ajn96/iSensor-SPI-Buffer/img/iSensor_spi_buffer_revb_bot.png

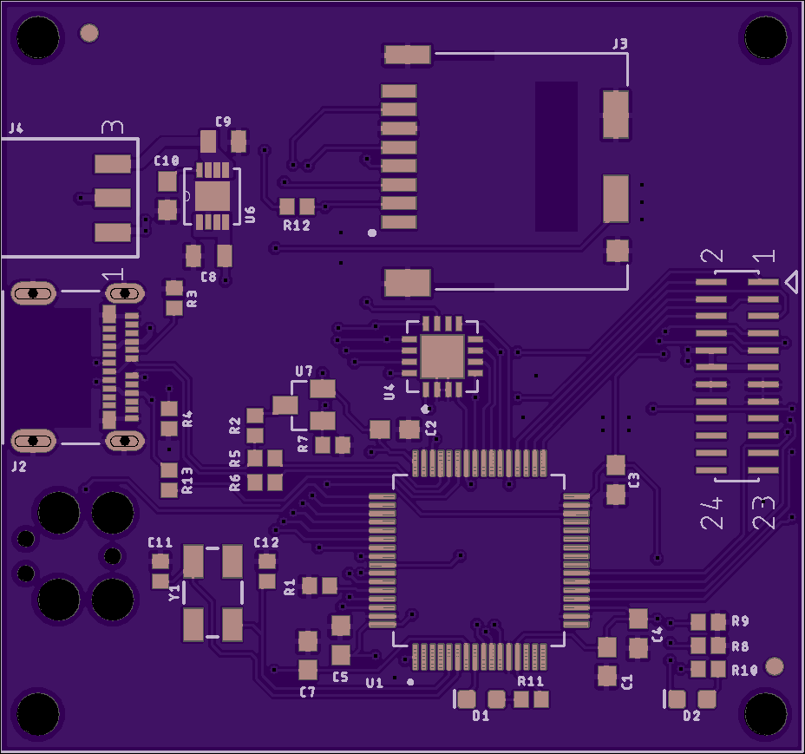
img/iSensor_spi_buffer_revb_bot.png
