ajn96/iSensor-SPI-Buffer/img/iso_image.jpg

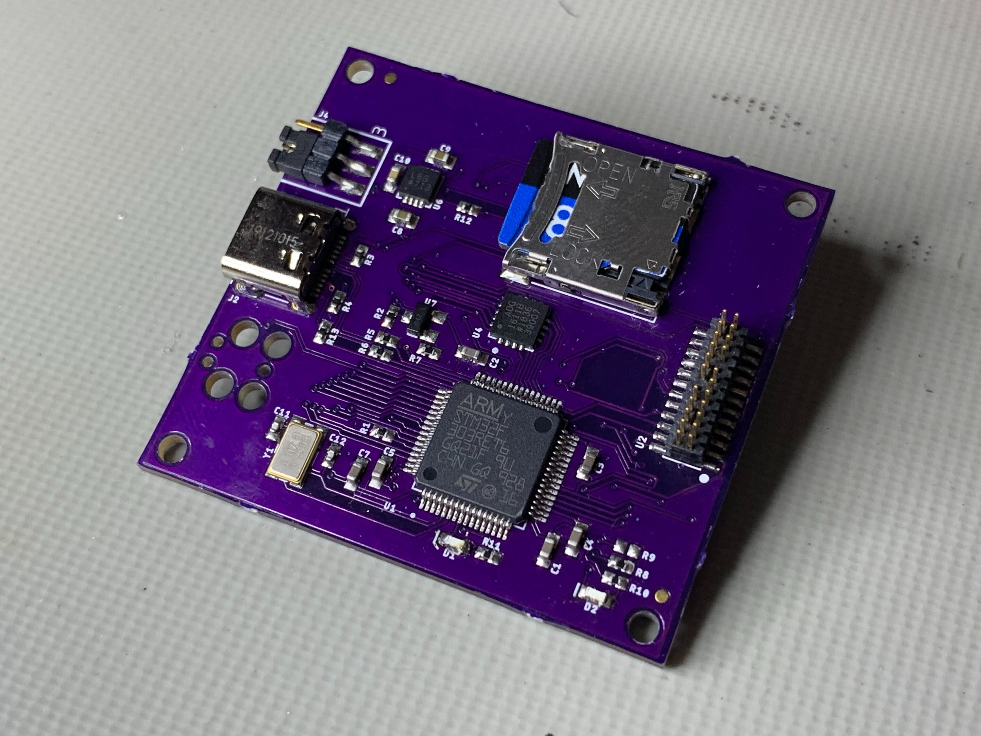
img/iso_image.jpg
