ajn96/iSensor-SPI-Buffer/img/rev_c_image.jpg

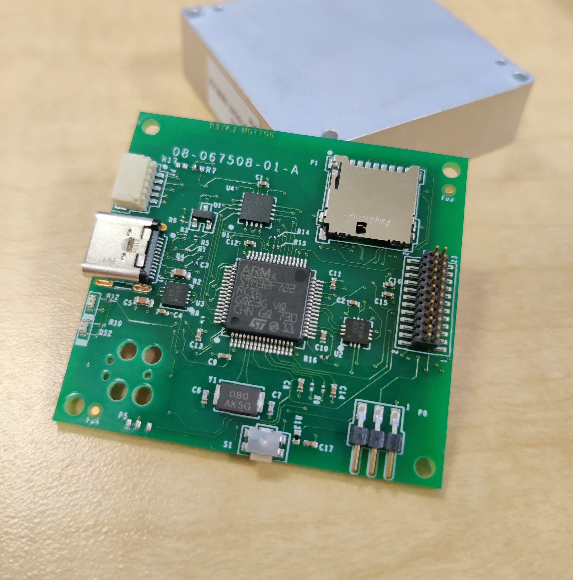
img/rev_c_image.jpg
