ajn96/iSensor-SPI-Buffer/img/usb_view.jpg

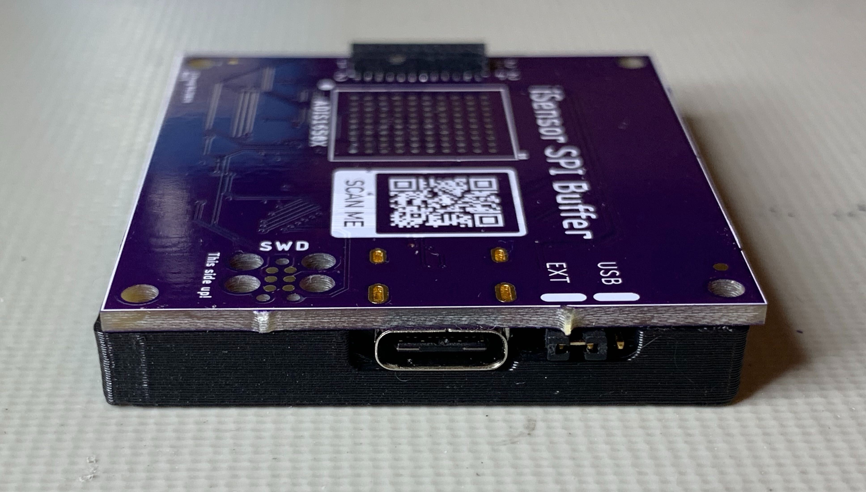
img/usb_view.jpg
