ajn96/iSensor-SPI-Buffer/firmware/Core/Src/isr.c

/**
  * Copyright (c) Analog Devices Inc, 2020
  * All Rights Reserved.
  *
  * @file		isr.c
  * @date		4/27/2020
  * @author		A. Nolan (alex.nolan@analog.com)
  * @brief		iSensor-SPI-Buffer interrupt service routines
 **/

#include "reg.h"
#include "imu.h"
#include "isr.h"
#include "buffer.h"
#include "user_spi.h"
#include "dio.h"
#include "flash.h"
#include "main.h"
#include "data_capture.h"
#include "timer.h"

/* Private function prototypes */
static void FinishImuBurst();
static void ProcessSPITransaction(uint32_t rx);

/** Current capture size (in 16 bit words). Global scope */
volatile uint32_t g_wordsPerCapture;

/** Track if there is currently a capture in progress */
volatile uint32_t g_captureInProgress = 0u;

/** Pointer to buffer element which is being populated */
static uint8_t* BufferElementHandle;

/** Pointer to buffer data signature within buffer element which is being populated */
static uint16_t* BufferSigHandle;

/** Track number of words captured within current buffer entry */
static volatile uint32_t WordsCaptured;

/** Buffer signature */
static uint32_t BufferSignature;

/** Flag to track if IMU burst DMA is done */
static volatile uint32_t ImuDMADone = 0;

/**
  * @brief IMU data ready ISR. Kicks off data capture process.
  *
  * @return void
  *
  * All four DIOx_Master pins map to this interrupt handler. Only one
  * should be enabled as an interrupt source at a time. This interrupt
  * also handles PPS input signals for DIO2-4. The EXTI pending interrupt
  * register (PR) can be used to identify if the interrupt is coming from
  * a PPS strobe or an IMU data ready signal.
  */
void EXTI9_5_IRQHandler()
{
	/* EXTI pending request register */
	static uint32_t EXTI_PR;

	/* Microsecond sample time stamp */
	static uint32_t SampleTimestampUs;

	/* Second sample time stamp */
	static uint32_t SampleTimestampS;

	/* Clear exti PR register (lines 5-9) */
	EXTI_PR = EXTI->PR;
	EXTI->PR = (0x1F << 5);

	/* Check if is PPS interrupt */
	if(EXTI_PR & (PPS_INT_MASK))
	{
		/* Increment PPS counter and clear microsecond timestamp */
		Timer_Increment_PPS_Time();
	}

	/* Exit if no data ready interrupt */
	if(!(EXTI_PR & (DATA_READY_INT_MASK)))
	{
		return;
	}

	/* If capture in progress then set error flag and exit */
	if(g_captureInProgress)
	{
		/* If SPI DMA and timer 4 are not running then capture is not actually in progress */
		if((g_dma_spi1_tx.Instance->CNDTR > 0)||(g_dma_spi1_rx.Instance->CNDTR > 0)||(TIM4->CR1 & 0x1))
		{
			g_captureInProgress = 1;
		}
		else
		{
			g_captureInProgress = 0;
		}
		g_regs[STATUS_0_REG] |= STATUS_OVERRUN;
		g_regs[STATUS_1_REG] = g_regs[STATUS_0_REG];
		return;
	}

	/* If buffer element cannot be added then exit */
	if(!Buffer_Can_Add_Element())
		return;

	/* Get the sample timestamp */
	SampleTimestampUs = Timer_Get_Microsecond_Timestamp();
	SampleTimestampS = Timer_Get_PPS_Timestamp();

	/* Get element handle */
	BufferElementHandle = Buffer_Add_Element();

	/* Add timestamp to buffer */
	*(uint32_t *) BufferElementHandle = SampleTimestampS;
	*(uint32_t *) (BufferElementHandle + 4) = SampleTimestampUs;

	/* Set signature to timestamp value initially */
	BufferSignature = SampleTimestampS & 0xFFFF;
	BufferSignature += (SampleTimestampS >> 16);
	BufferSignature += SampleTimestampUs & 0xFFFF;
	BufferSignature += (SampleTimestampUs >> 16);

	/* Set buffer signature handle */
	BufferSigHandle = (uint16_t *) (BufferElementHandle + 8);

	/* Offset buffer element handle by 10 bytes (timestamp + sig) */
	BufferElementHandle += 10;

	/* Set flag indicating capture is running */
	g_captureInProgress = 1;

	if(g_regs[BUF_CONFIG_REG] & BUF_CFG_IMU_BURST)
	{
		ImuDMADone = 0;
		IMU_Start_Burst(BufferElementHandle);
	}
	else
	{
		/* Register SPI data capture */

		/* Set words captured to 0 */
		WordsCaptured = 0;

		/*Set timer value to 0 */
		TIM4->CNT = 0;
		/* Enable timer */
		TIM4->CR1 |= 0x1;
		/* Clear timer interrupt flag */
		TIM4->SR &= ~TIM_SR_UIF;

		/* Send first 16 bit word */
		TIM3->CR1 &= ~0x1;
		TIM3->CNT = 0;
		TIM3->CR1 |= 0x1;
		SPI1->DR = g_regs[BUF_WRITE_0_REG];
	}
}

/**
  * @brief EXTI 4 interrupt handler.
  *
  * @return void
  *
  * This interrupt is generated by a PPS signal applied to
  * DIO1 only. All other PPS inputs generate an EXTI9_5 interrupt
  */
void EXTI4_IRQHandler()
{
	/* Clear pending interrupts */
	EXTI->PR = (1 << 4);

	/* Increment PPS timestamp */
	Timer_Increment_PPS_Time();
}

/**
  * @brief IMU SPI timer ISR.
  *
  * @return void
  *
  * This interrupt retrieves the SPI data read on the previous SPI transaction. It
  * then starts the next SPI transaction (if needed) and returns.
  */
void TIM4_IRQHandler()
{
	/** SPI MISO data */
	static uint32_t SpiMiso;

	/* Clear timer interrupt flag */
	TIM4->SR &= ~TIM_SR_UIF;

	/* Reset timer count. Want to reset it to give a ~0.7us offset */
	TIM4->CNT = 50;

	/* Disable CS timer */
	TIM3->CR1 = 0;
	TIM3->CNT = 0xFFFF;

	if(!g_captureInProgress)
	{
		/* Disable timers */
		TIM4->CR1 &= ~0x1;
		return;
	}

	/* Wait for SPI rx done (running in master mode, shouldn't be an issue) */
	while(!(SPI1->SR & SPI_SR_RXNE));

	/* Grab SPI data from last transaction */
	SpiMiso = SPI1->DR;

	/* Add to signature */
	BufferSignature += SpiMiso;

	BufferElementHandle[0] = (SpiMiso & 0xFF);
	BufferElementHandle[1] = (SpiMiso >> 8);
	BufferElementHandle += 2;

	/* Increment words captured count */
	WordsCaptured++;

	if(WordsCaptured < g_wordsPerCapture)
	{
		/* Restart PWM timer for CS */
		TIM3->CR1 |= 0x1;
		/* Load SPI transmit reg */
		SPI1->DR = g_regs[BUF_WRITE_0_REG + WordsCaptured];
	}
	else
	{
		/* Disable timers and ensure CS is high */
		TIM4->CR1 &= ~0x1;
		TIM3->CR1 &= ~0x1;
		TIM3->CNT = 0xFFFF;

		/* Save final signature */
		BufferSigHandle[0] = BufferSignature;

		/* Update buffer count regs with new count */
		g_regs[BUF_CNT_0_REG] = g_bufCount;
		g_regs[BUF_CNT_1_REG] = g_regs[BUF_CNT_0_REG];

		/* Mark capture as done */
		g_captureInProgress = 0;
	}
}

/**
  * @brief This function handles DMA1 channel2 global interrupt (spi1 (IMU) Rx).
  *
  * @return void
  *
  * This DMA is used to receive data from an IMU during a burst data capture.
  * In order for an IMU data capture to be complete, this DMA channel and the
  * transmit DMA channel have to both finish their work. In general, this channel
  * will finish last.
  **/
void DMA1_Channel2_IRQHandler(void)
{
	uint32_t flags = g_dma_spi1_rx.DmaBaseAddress->ISR;

	/* Clear interrupt enable */
	g_dma_spi1_rx.Instance->CCR &= ~(DMA_IT_TC | DMA_IT_TE);

	/* Clear interrupt flags */
	g_dma_spi1_rx.DmaBaseAddress->IFCR = (DMA_FLAG_TC1|DMA_FLAG_TE1) << g_dma_spi1_rx.ChannelIndex;

	/* Check for error interrupt */
	if(flags & (DMA_FLAG_TE1 << g_dma_spi1_rx.ChannelIndex))
	{
		g_regs[STATUS_0_REG] |= STATUS_DMA_ERROR;
		g_regs[STATUS_1_REG] = g_regs[STATUS_0_REG];
		FinishImuBurst();
	}

	/* Check if both interrupts complete */
	if(ImuDMADone == 0)
	{
	  ImuDMADone = 1;
	}
	else
	{
	  /* Both are done */
	  FinishImuBurst();
	}
}

/**
  * @brief This function handles DMA1 channel3 global interrupt (spi1 (IMU) Tx).
  *
  * @return void
  *
  * This DMA is used to transmit the write data array to the IMU during a burst
  * data capture. It runs in parallel with DMA channel 2 to achieve full duplex burst.
  */
void DMA1_Channel3_IRQHandler(void)
{
	uint32_t flags = g_dma_spi1_tx.DmaBaseAddress->ISR;

	/* Clear interrupt enable */
	g_dma_spi1_tx.Instance->CCR &= ~(DMA_IT_TC | DMA_IT_TE);

	/* Clear interrupt flags */
	g_dma_spi1_tx.DmaBaseAddress->IFCR = (DMA_FLAG_TC1|DMA_FLAG_TE1) << g_dma_spi1_tx.ChannelIndex;

	/* Check for error interrupt */
	if(flags & (DMA_FLAG_TE1 << g_dma_spi1_tx.ChannelIndex))
	{
		g_regs[STATUS_0_REG] |= STATUS_DMA_ERROR;
		g_regs[STATUS_1_REG] = g_regs[STATUS_0_REG];
		FinishImuBurst();
	}

	/* Check if both interrupts complete */
	if(ImuDMADone == 0)
	{
	  ImuDMADone = 1;
	}
	else
	{
	  FinishImuBurst();
	}
}

/**
  * @brief Cleans up an IMU burst data read
  *
  * @return void
  *
  * This function is called once the SPI1 Tx and Rx DMA interrupts
  * have both fired, or a single error interrupt has been generated.
  * SPI1 uses DMA1, channel 2/3. These channels have lower priority
  * than the user SPI DMA channels, which also use DMA peripheral 1.
  *
  * This function brings CS high, calculates the buffer signature,
  * and updates the buffer count / capture state variables. Before
  * this function is called, DMA interrupts should be disabled (by
  * their respective ISR's)
  */
static void FinishImuBurst()
{
	/* Bring CS high */
	TIM3->CR1 &= ~0x1;
	TIM3->CNT = 0xFFFF;

	/* Build buffer signature */
	uint16_t * RxData = (uint16_t *) BufferElementHandle;
	for(int reg = 0; reg < (g_regs[BUF_LEN_REG] / 2); reg++)
	{
		BufferSignature += RxData[reg];
	}
	/* Save signature to buffer entry */
	BufferSigHandle[0] = BufferSignature;

	/* Update buffer count regs with new count */
	g_regs[BUF_CNT_0_REG] = g_bufCount;
	g_regs[BUF_CNT_1_REG] = g_regs[BUF_CNT_0_REG];

	/* Mark capture as done */
	g_captureInProgress = 0;
}

/**
  * @brief This function handles DMA1 channel5 global interrupt (spi2 (user) Tx).
  *
  * @return void
  *
  * This interrupt is only used to flag errors. Ending a buffer burst output is
  * triggered by an EXTI interrupt attached to chip select.
  */
void DMA1_Channel5_IRQHandler(void)
{
	uint32_t flags = g_dma_spi2_tx.DmaBaseAddress->ISR;

	/* Clear interrupt enable */
	g_dma_spi2_tx.Instance->CCR &= ~DMA_IT_TE;

	/* Clear interrupt flags */
	g_dma_spi2_tx.DmaBaseAddress->IFCR = (DMA_FLAG_TE1|DMA_FLAG_TC1|DMA_FLAG_HT1) << g_dma_spi2_tx.ChannelIndex;

	/* Check for error interrupt */
	if(flags & (DMA_FLAG_TE1 << g_dma_spi2_tx.ChannelIndex))
	{
		/* Flag DMA error */
		g_regs[STATUS_0_REG] |= STATUS_DMA_ERROR;
		g_regs[STATUS_1_REG] = g_regs[STATUS_0_REG];
	}
}

/**
  * @brief This function handles the user SPI (SPI2) rx data interrupt
  *
  * @return void
  *
  * The SPI Rx data interrupt is used for standard register reads. The SPI2
  * peripheral is configured to generate an interrupt once two bytes of data
  * have been received.
  *
  * IMPORTANT NOTE: Due to data packing, each read from the SPI data register
  * actually pulls two bytes from the Rx FIFO. These bytes are in reversed
  * order from how they were received on the bus. For more information on this
  * behavior, see the data packing section of the SPI entry in the technical
  * reference manual.
  *
  * If a burst read is requested, this interrupt is disabled, and the CS
  * rising edge interrupt is enabled instead. This allows for variable length
  * burst read transactions. The hand off from register mode to burst mode and
  * back requires special care. We want to avoid potential issues if the user
  * just immediately starts full length burst reads, rather than requesting a burst
  * first. We essentially have to wait for the current SPI transaction
  * to finish before enabling the burst. Otherwise, the burst can potentially get
  * enabled half way through this transfer, which messes up the whole burst read
  * sequence. We could accomplish this by polling CS in the ISR, but that has
  * a strong potential to mess with other functionality (user SPI interrupt is
  * highest priority, and also generally polling in an ISR is a bad idea). Instead,
  * a flag is set, which must be cleared by the CS ISR. This flag is checked
  * by the buffer dequeue routine which runs from the main loop.
  *
  * Once no more bursts are requested, the SPI2
  * interrupt will be re-enabled through the user SPI burst disable function.
  */
void SPI2_IRQHandler(void)
{
	/* Error occured */
	uint32_t error = 0u;

	/* SPI status register */
	uint32_t spiSr;

	/* Rx data */
	uint32_t rx;

	/* Read SPI2 SR to clear flags */
	spiSr = SPI2->SR;

	/* Grab Rx data */
	rx = SPI2->DR;

	/* Are we starting a burst read? */
	if(Reg_Is_Burst_Read(rx & 0xFFu))
	{
		/* Set flag for buffer dequeue. Increases coupling, but oh well */
		g_update_flags |= DEQUEUE_BUF_FLAG;
		/* Disable SPI interrupts immediately */
		NVIC_DisableIRQ(SPI2_IRQn);
		/* Set flag indicating burst start and enable CS interrupt */
		g_user_burst_start = 1u;
		NVIC_ClearPendingIRQ(EXTI15_10_IRQn);
		NVIC_EnableIRQ(EXTI15_10_IRQn);
		/* Exit early */
		return;
	}

	/* More than two bytes received? Then flag error and reset SPI */
	if ((spiSr & SPI_FRLVL_FULL) == SPI_FRLVL_FULL)
	{
		error = 1u;
	}

	/* Error interrupt source. This can be a mode fault, overrun, or underrun */
	if(spiSr & (SPI_FLAG_OVR | SPI_FLAG_MODF | SPI_SR_UDR))
	{
		error = 1u;
	}

	/* If there is still Tx data then an error has occurred */
	if(spiSr & SPI_SR_FTLVL)
	{
		error = 1u;
	}

	/* Has an error occurred? */
	if (error != 0u)
	{
		/* Flag error */
		g_regs[STATUS_0_REG] |= STATUS_SPI_OVERFLOW;
		g_regs[STATUS_1_REG] = g_regs[STATUS_0_REG];

		/* Re-init SPI to make sure we end up in a good state */
		User_SPI_Reset(true);
		/* Load single word to transmit */
		SPI2->DR = 0u;
	}
	else
	{
		/* Handle transaction */
		ProcessSPITransaction(rx);
	}
	/* Clear EXTI PR register (lines 10-15) */
	EXTI->PR = USER_SPI_CS_INT_MSK;
}

/**
  * @brief This function handles the user SPI (SPI2) chip select rising edge
  *
  * @return void
  *
  * Two interrupts are used for the user SPI interface. In register mode, the
  * SPI2 interrupt is used to interrupt when two bytes are received, to avoid an
  * unnecessary dependency on the CS state (caused issues for some Linux systems
  * which like to toggle CS after each byte). This interrupt is used when in
  * burst mode only. In burst mode, a variable number of bytes is clocked out, so
  * the CS rising edge must be used to delimit the end of a transaction.
  *
  * In this interrupt, if another burst read is requested, the CS rising edge
  * interrupt is kept enabled, and the buffer board is configured for another burst.
  * If a standard register read/write is requested, then the CS interrupt is
  * disabled, and the standard SPI interrupt re-enabled.
  *
  * When this function is called, the SPI should be operating in 16-bit mode, rather
  * than the 8-bit mode used for register interfacing.
  */
void EXTI15_10_IRQHandler(void)
{
	/* SPI data */
	uint32_t rx, tx;

	/* Clear EXTI PR register (lines 10-15) */
	EXTI->PR = USER_SPI_CS_INT_MSK;

	/* First CS posedge after burst read request? */
	if(g_user_burst_start != 0u)
	{
		g_user_burst_start = 0u;
		return;
	}

	/* Read first SPI data word received */
	rx = SPI2->DR;

	/* If a burst is running disable DMA and re-init SPI */
	if(g_userburstRunning)
	{
		/* Disable DMA */
		g_dma_spi2_tx.Instance->CCR &= ~DMA_CCR_EN;

		/* Clear burst running flag */
		g_userburstRunning = 0;

		/* Are we no longer in burst mode? */
		if((rx & 0xFF00) != 0x0600)
		{
			/* Exit burst mode */
			User_SPI_Burst_Disable();
			/* We are now back in 8-bit mode, need to accommodate by
			 * swapping around the Rx bytes */
			tx = (rx << 8u) & 0xFF00u;
			rx = (rx >> 8u) & 0xFFu;
			rx |= tx;
			/* Handle SPI transaction */
			ProcessSPITransaction(rx);
		}
		/* We must be reading another burst */
		else
		{
			/* Set flag for additional burst read */
			g_update_flags |= DEQUEUE_BUF_FLAG;
		}
	}
	/* Burst not running means this interrupt should not be enabled */
	else
	{
		/* This should not happen, flag error */
		g_regs[STATUS_0_REG] |= STATUS_SPI_OVERFLOW;
		/* Get SPI back to good state */
		User_SPI_Burst_Disable();
		/* Load single word to transmit */
		SPI2->DR = 0u;
	}
}

/**
  * @brief Process a 16 bit data word from the user SPI
  *
  * @param rx Two bytes from the user SPI in register mode, packed
  *
  * @return void
  *
  * This function accommodates for the swapped endianess of bytes which
  * are packed into the SPI Rx data register.
  *
  * If the value on the SPI bus is: 0x1234, then the data register
  * will hold 0x3412. This is true for both receive and transmit.
  *
  * IMPORTANT: This should only be used for register mode, when
  * the SPI data word size is 8 bits. In burst mode, where the SPI
  * data word size is 16 bits, this will not work, since data packing
  * is not used.
  */
static void ProcessSPITransaction(uint32_t rx)
{
	uint16_t txData;
	/* Is write requested? */
	if(rx & 0x0080u)
	{
		/* Write */
		txData = Reg_Write(rx & 0x7F, rx >> 8u);
	}
	else
	{
		/* Read */
		txData = Reg_Read(rx & 0x7F);
	}

	/* Transmit data back, swap endianness. This is done to account for
	 * automatic byte packing when in byte-mode */
	SPI2->DR = (txData << 8u) | (txData >> 8u);
}

/**
  * @brief This function handles Hard fault interrupt.
  *
  * @return void
  */
void HardFault_Handler(void)
{
	/* Store error message for future retrieval and reboot */
	Flash_Log_Fault(ERROR_HARDFAULT);
	NVIC_SystemReset();
}

/**
  * @brief This function handles Memory management fault.
  *
  * @return void
  */
void MemManage_Handler(void)
{
	/* Store error message for future retrieval and reboot */
	Flash_Log_Fault(ERROR_MEM);
	NVIC_SystemReset();
}

/**
  * @brief This function handles Pre-fetch fault, memory access fault.
  *
  * @return void
  */
void BusFault_Handler(void)
{
	/* Store error message for future retrieval and reboot */
	Flash_Log_Fault(ERROR_BUS);
	NVIC_SystemReset();
}

/**
  * @brief This function handles Undefined instruction or illegal state.
  *
  * @return void
  */
void UsageFault_Handler(void)
{
	/* Store error message for future retrieval and reboot */
	Flash_Log_Fault(ERROR_USAGE);
	NVIC_SystemReset();
}
