ajn96/iSensor-SPI-Buffer/firmware/Core/Inc/data_capture.h

/**
  * Copyright (c) Analog Devices Inc, 2020
  * All Rights Reserved.
  *
  * @file		data_capture.h
  * @date		4/24/2020
  * @author		A. Nolan (alex.nolan@analog.com)
  * @brief		Header file for iSensor-SPI-Buffer autonomous IMU data acquisition module
 **/

#ifndef INC_DATA_CAPTURE_H_
#define INC_DATA_CAPTURE_H_

/* Public function prototypes */

/* @cond DOXYGEN_IGNORE */
void Data_Capture_Enable();
void Data_Capture_Disable();
/* @endcond */

#endif /* INC_DATA_CAPTURE_H_ */
