ajn96/iSensor-SPI-Buffer/firmware/Core/Inc/dfu.h

/**
  * Copyright (c) Analog Devices Inc, 2020
  * All Rights Reserved.
  *
  * @file		dfu.h
  * @date		10/9/2020
  * @author		A. Nolan (alex.nolan@analog.com)
  * @brief		Header file for iSensor-SPI-Buffer runtime firmware upgrade module
 **/

#ifndef INC_DFU_H_
#define INC_DFU_H_

/* Header includes require for prototypes */
#include <stdint.h>

/* Public function prototypes */

/* @cond DOXYGEN_IGNORE */
void DFU_Check_Flags();
void DFU_Prepare_Reboot();
/* @endcond */

/** Key to indicate DFU reboot is required. Set at DFU Flag location in SRAM */
#define ENABLE_DFU_KEY		0xA5A51234

/** Address in SRAM where the DFU key is written to indicate DFU reboot required */
#define DFU_FLAG_ADDR		(volatile uint32_t *) 0x2000FFFC

#endif /* INC_DFU_H_ */
