ajn96/iSensor-SPI-Buffer/firmware/Core/Inc/watchdog.h

/**
  * Copyright (c) Analog Devices Inc, 2020
  * All Rights Reserved.
  *
  * @file		watchdog.h
  * @date		4/30/2020
  * @author		A. Nolan (alex.nolan@analog.com)
  * @brief		Header file for iSensor-SPI-Buffer watchdog timer module
 **/

#ifndef INC_WATCHDOG_H_
#define INC_WATCHDOG_H_

/* Header includes require for prototypes */
#include <stdint.h>

/* Public function prototypes */

/* @cond DOXYGEN_IGNORE */
void Watchdog_Check_Status();
void Watchdog_Feed();
void Watchdog_Enable(uint32_t timeout_ms);
/* @endcond */

/** Watchdog base freq (40KHz) */
#define WATCHDOG_BASE_FREQ		40000

/** Watchdog key register write value to reload watchdog timer */
#define WATCHDOG_RELOAD_KEY		0x0000AAAA

/** Watchdog key register write value to start watchdog timer */
#define WATCHDOG_START_KEY		0x0000CCCC

/** Watchdog key register write value to unlock watchdog timer */
#define WATCHDOG_UNLOCK_KEY		0x00005555

#endif /* INC_WATCHDOG_H_ */
