ajn96/iSensor-SPI-Buffer/firmware/Core/Src/watchdog.c

/**
  * Copyright (c) Analog Devices Inc, 2020
  * All Rights Reserved.
  *
  * @file		watchdog.c
  * @date		4/30/2020
  * @author		A. Nolan (alex.nolan@analog.com)
  * @brief		iSensor-SPI-Buffer watchdog reset timer module implementation
 **/

#include "reg.h"
#include "watchdog.h"
#include "stm32f3xx_hal.h"
#include "stm32f303xe.h"

/**
  * @brief Feeds the watchdog timer. Should be called periodically from main loop
  *
  * @return void
  *
  * If this function is not called within the reset period, the watchdog timer will
  * trip and force a system reset. Default watchdog timeout is 2s, which should be
  * significantly longer than any operation execution time in firmware.
  */
void Watchdog_Feed()
{
	IWDG->KR = WATCHDOG_RELOAD_KEY;
}

/**
  * @brief Check if system reset from independent watch dog timeout and sets the appropriate STATUS flag
  *
  * @return void
  */
void Watchdog_Check_Status()
{
	if(__HAL_RCC_GET_FLAG(RCC_FLAG_IWDGRST))
	{
		g_regs[STATUS_0_REG] |= STATUS_WATCHDOG;
		g_regs[STATUS_1_REG] = g_regs[STATUS_0_REG];
	}
}

/**
  * @brief Enables watch dog reset functionality
  *
  * @param timeout_ms The watch dog reset time (in ms)
  *
  * This functions calculates the watch dog time base based on
  * desired timeout, to give the best granularity. The STM32
  * independent watch dog peripheral runs on a 40KHz RC oscillator.
  * This 40KHz clock can be divided down in range 4 - 256. The
  * watchdog itself resets the system when the watchdog timer reaches
  * a value of 0 (12 bit counter).
  *
  * Min timeout (highest resolution): 4095 / (40KHz / 4) -> 0.410s
  *
  * Max timeout: 4095 / (40KHz / 256) -> 26.2s
  */
void Watchdog_Enable(uint32_t timeout_ms)
{
	/* Watchdog scaled freq */
	uint32_t scaledFreq;

	/* Reg values to write */
	uint32_t scale, reloadVal;

	/* cap at 26.2 s*/
	if(timeout_ms > 26200)
	{
		timeout_ms = 26200;
	}

	/* Set scaler value based on timeout */
	if(timeout_ms < 490)
	{
		scaledFreq = WATCHDOG_BASE_FREQ / 4;
		scale = 0;
	}
	else if(timeout_ms < 819)
	{
		scaledFreq = WATCHDOG_BASE_FREQ / 8;
		scale = 1;
	}
	else if(timeout_ms < 1638)
	{
		scaledFreq = WATCHDOG_BASE_FREQ / 16;
		scale = 2;
	}
	else if(timeout_ms < 3276)
	{
		scaledFreq = WATCHDOG_BASE_FREQ / 32;
		scale = 3;
	}
	else if(timeout_ms < 6552)
	{
		scaledFreq = WATCHDOG_BASE_FREQ / 64;
		scale = 4;
	}
	else if(timeout_ms < 13104)
	{
		scaledFreq = WATCHDOG_BASE_FREQ / 128;
		scale = 5;
	}
	else
	{
		scaledFreq = WATCHDOG_BASE_FREQ / 256;
		scale = 6;
	}

	/* Set reload value based on freq times timeout */
	reloadVal = ((scaledFreq * timeout_ms) / 1000) + 1;

	/* Enable watchdog */
	IWDG->KR = WATCHDOG_START_KEY;

	/* Unlock watchdog peripheral writes */
	IWDG->KR = WATCHDOG_UNLOCK_KEY;

	/* Set period scaler register */
	IWDG->PR = scale;

	/* Set reload register */
	IWDG->RLR = reloadVal;

	/* Wait for done */
	while(IWDG->SR);

	/* Initial clear */
	Watchdog_Feed();
}
